xjjak/LapCal/Documentation/images/battery-values-terminal-screenshot.png

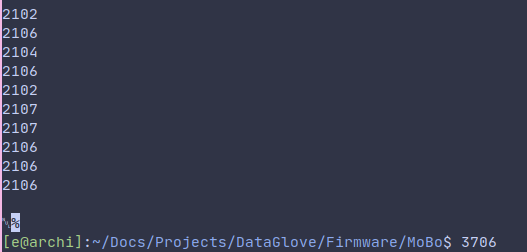
Documentation/images/battery-values-terminal-screenshot.png
