xjjak/LapCal/Documentation/images/differential-pair-calculations.png

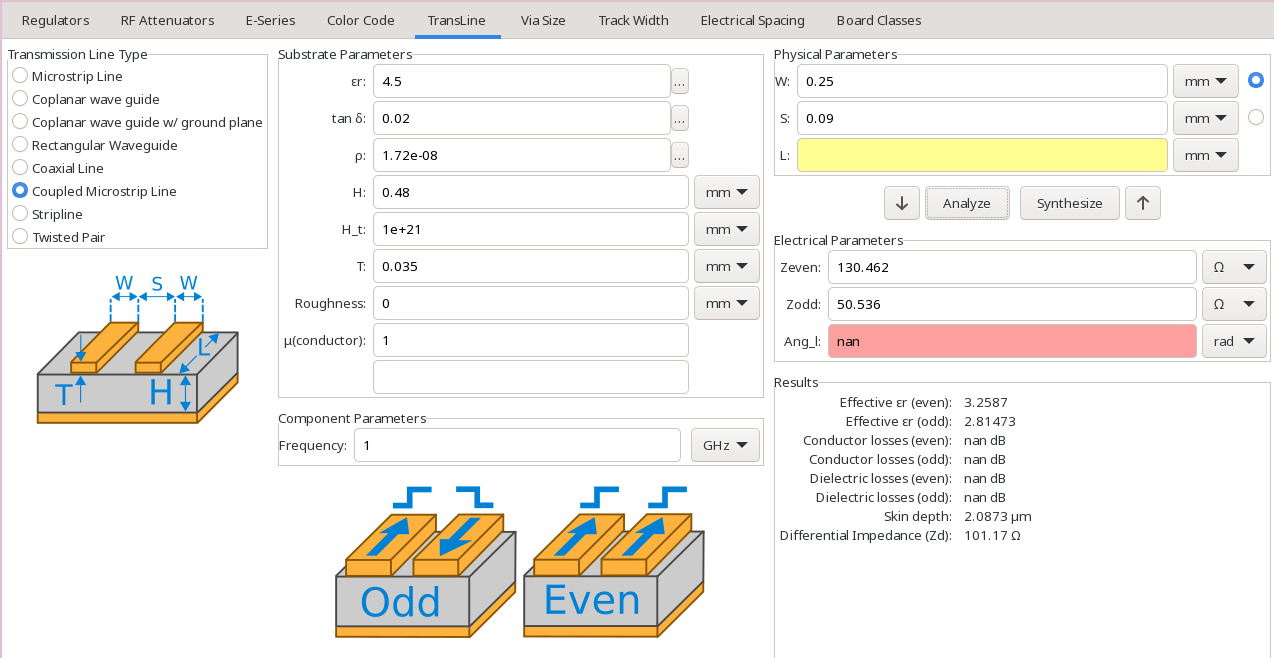
Documentation/images/differential-pair-calculations.png
