xjjak/LapCal/Documentation/images/motherboard_3dfront.png

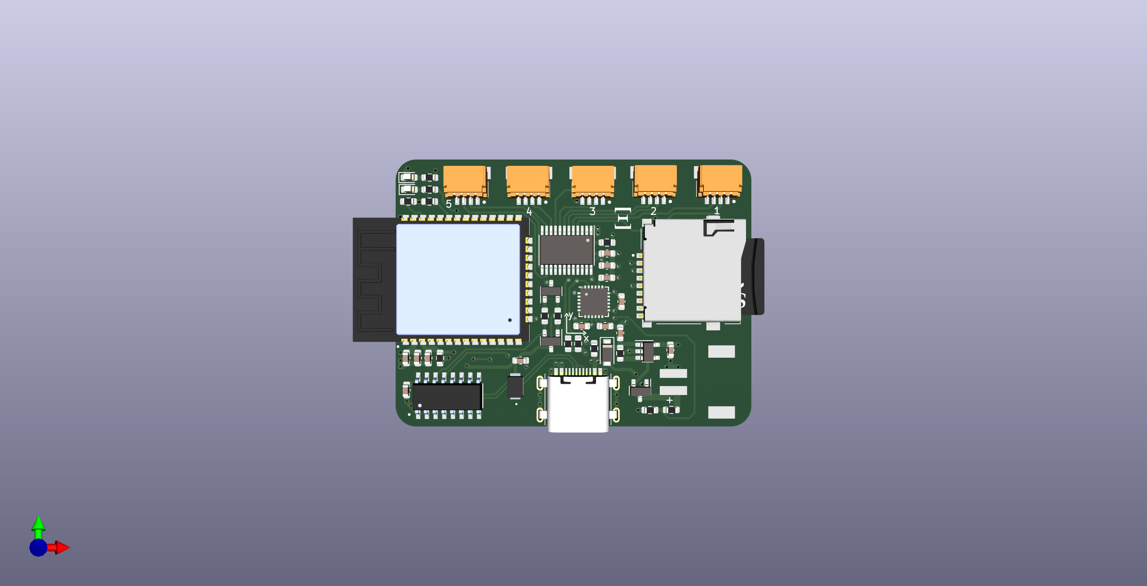
Documentation/images/motherboard_3dfront.png
