xjjak/LapCal/Software/diagrams/ema_centering/compare_1.png

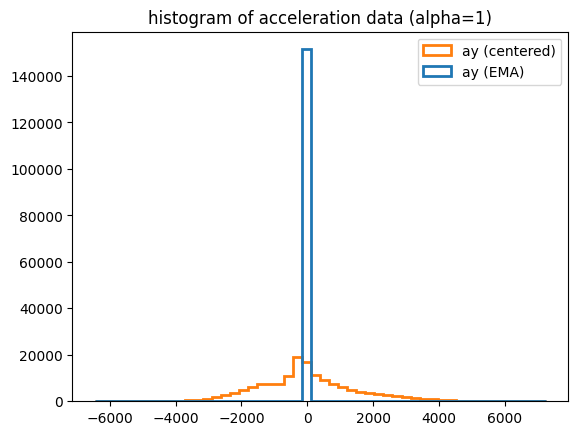
Software/diagrams/ema_centering/compare_1.png
