xjjak/LapCal/Hardware/Electronics/motherboard/motherboard/parts/TYPE-C-31-M-14_C223907/hro-usb-type-c-31-m-14-1/2021-02-06_20-00-18.png

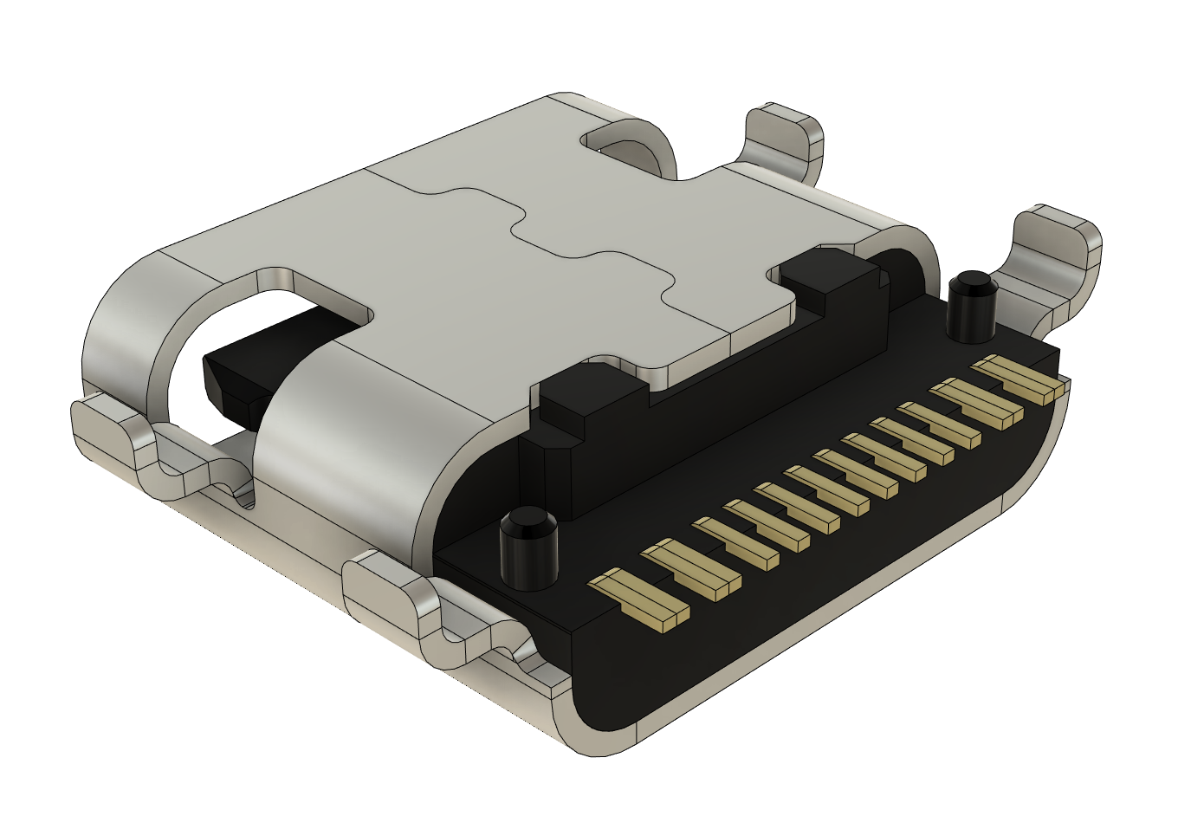
Hardware/Electronics/motherboard/motherboard/parts/TYPE-C-31-M-14_C223907/hro-usb-type-c-31-m-14-1/2021-02-06_20-00-18.png
