xjjak/LapCal/Hardware/Firmware/mainboard/include/sensors.h

void setup_i2c(int sda, int scl);
int setup_sensor(int id);
void setup_sensors();
// reading sense_readings(MPU6050 mpu);
void get_all_readings(reading* output);
void format_readings(reading* input, char* output_buf, uint64_t timestamp);
void task_fifo_reset(void *pvParameters);
